mzandrew/jabberwocky-oscilloscope/images/2009-05-30.16_30_52.canon-s70.00823.first-light.first-jabberwocky-lab3-data-hexdump.jpeg

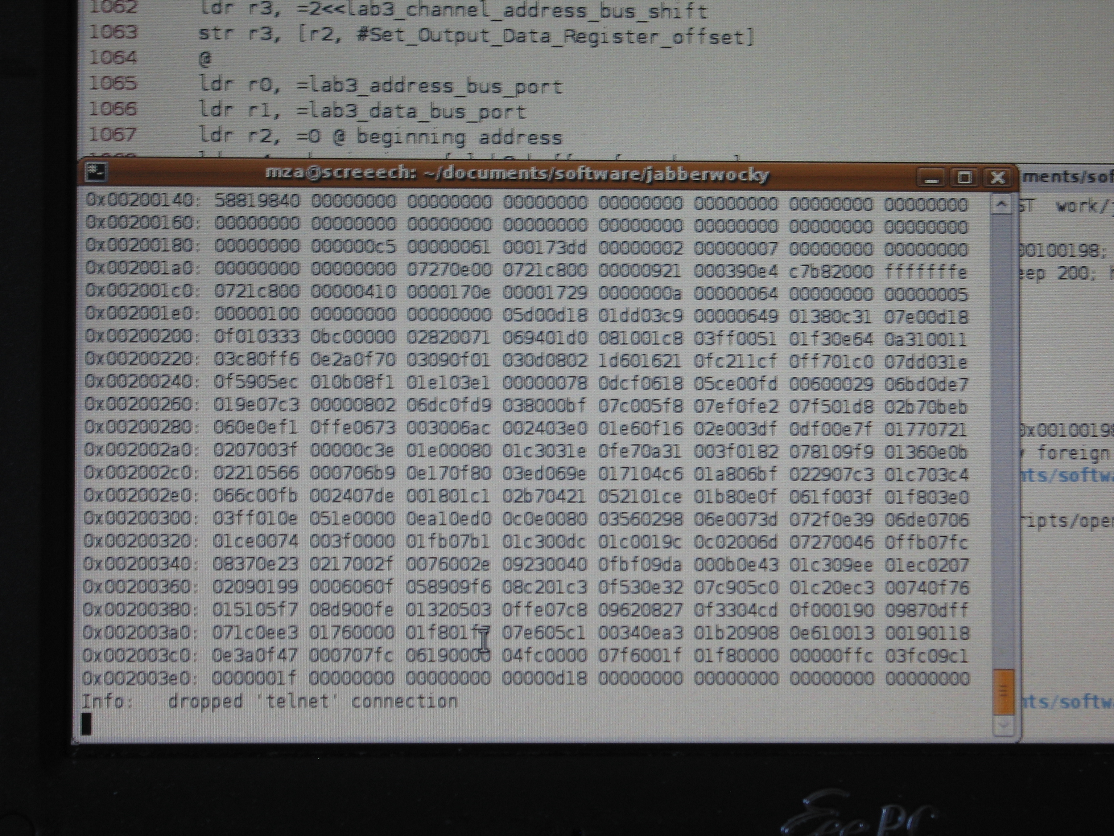
images/2009-05-30.16_30_52.canon-s70.00823.first-light.first-jabberwocky-lab3-data-hexdump.jpeg
