mzandrew/jabberwocky-oscilloscope/images/2009-06-07.18_14_04.canon-s70.00827.first-light.first-jabberwocky-scope-trace.jpeg

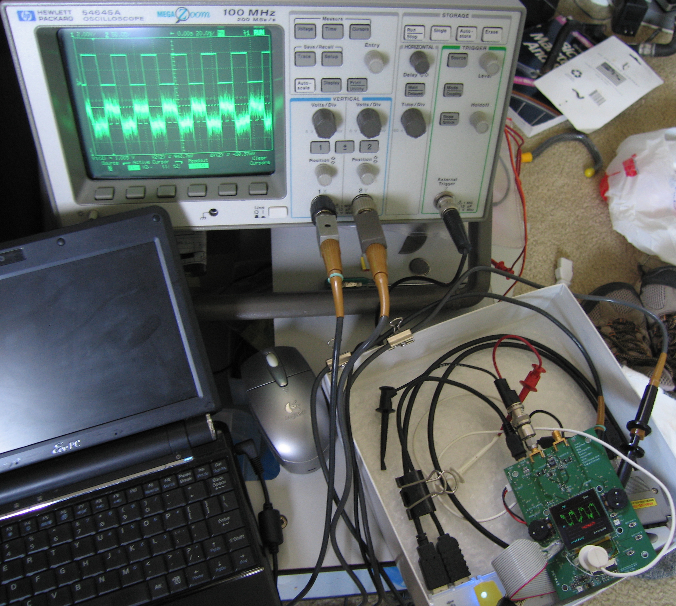
images/2009-06-07.18_14_04.canon-s70.00827.first-light.first-jabberwocky-scope-trace.jpeg
