mzandrew/jabberwocky-oscilloscope/images/2009-06-07.18_14_17.canon-s70.00828.first-light.second-jabberwocky-scope-trace.jpeg

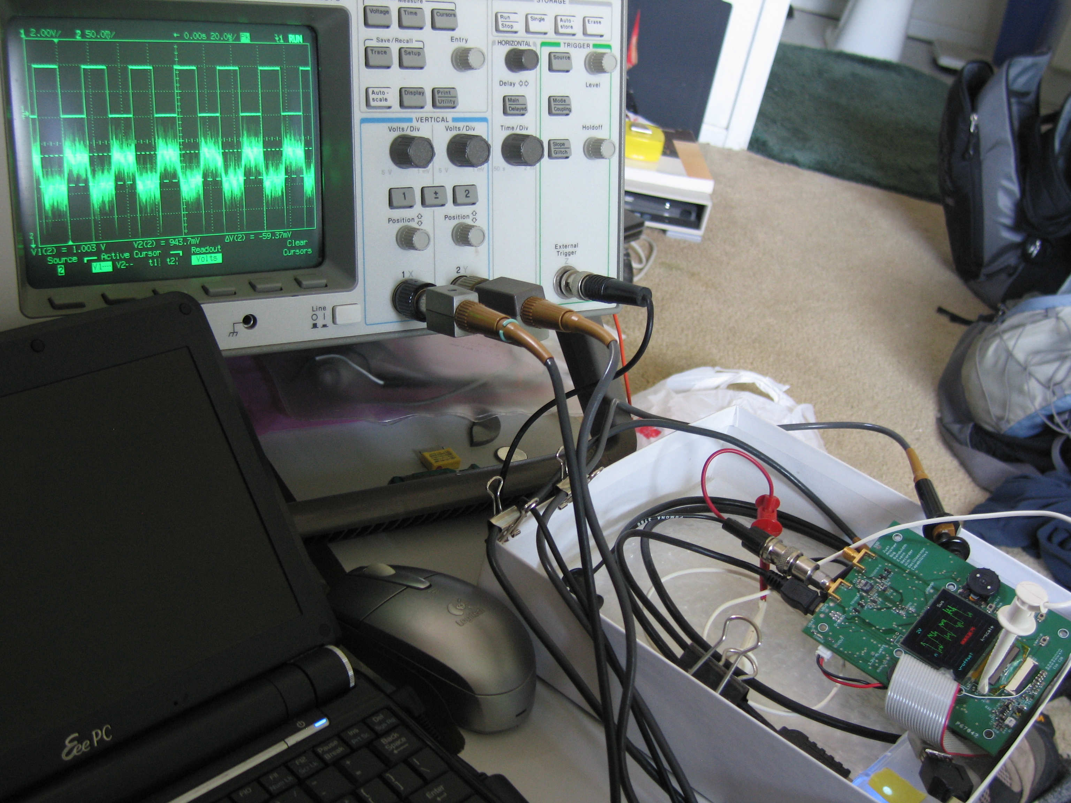
images/2009-06-07.18_14_17.canon-s70.00828.first-light.second-jabberwocky-scope-trace.jpeg
